kynjo/DRUM_2026_AI/tablesESP32_E.h

//  Tables V4

//This table id compatible with 20000.00 Hz. sampling rate
//Envelope frequency tuning word vs. MIDI range value [0-127]
const uint16_t EFTWS[]={
0x0371,0x0340,0x0311,0x02E5,0x02BB,0x0294,0x026F,0x024C,0x022B,0x020C,0x01EE,0x01D3,0x01B8,0x01A0,0x0188,0x0172,
0x015D,0x014A,0x0137,0x0126,0x0115,0x0106,0x00F7,0x00E9,0x00DC,0x00D0,0x00C4,0x00B9,0x00AE,0x00A5,0x009B,0x0093,
0x008A,0x0083,0x007B,0x0074,0x006E,0x0068,0x0062,0x005C,0x0057,0x0052,0x004D,0x0049,0x0045,0x0041,0x003D,0x003A,
0x0037,0x0034,0x0031,0x002E,0x002B,0x0029,0x0026,0x0024,0x0022,0x0020,0x001E,0x001D,0x001B,0x001A,0x0018,0x0017,
0x0015,0x0014,0x0013,0x0012,0x0011,0x0010,0x000F,0x000E,0x000D,0x000D,0x000C,0x000B,0x000A,0x000A,0x0009,0x0009,
0x0008,0x0008,0x0007,0x0007,0x0006,0x0006,0x0006,0x0005,0x0005,0x0005,0x0004,0x0004,0x0004,0x0004,0x0003,0x0003,
0x0003,0x0003,0x0003,0x0002,0x0002,0x0002,0x0002,0x0002,0x0002,0x0002,0x0001,0x0001,0x0001,0x0001,0x0001,0x0001,
0x0001,0x0001,0x0001,0x0001,0x0001,0x0001,0x0000,0x0000,0x0000,0x0000,0x0000,0x0000,0x0000,0x0000,0x0000,0x0000,
};

//Voice frequency tuning word vs. MIDI note [0-127]
const uint16_t PITCHS[]={
0x001A,0x001C,0x001E,0x001F,0x0021,0x0023,0x0025,0x0028,0x002A,0x002D,0x002F,0x0032,0x0035,0x0038,0x003C,0x003F,
0x0043,0x0047,0x004B,0x0050,0x0055,0x005A,0x005F,0x0065,0x006B,0x0071,0x0078,0x007F,0x0087,0x008F,0x0097,0x00A0,
0x00AA,0x00B4,0x00BE,0x00CA,0x00D6,0x00E3,0x00F0,0x00FE,0x010E,0x011E,0x012F,0x0141,0x0154,0x0168,0x017D,0x0194,
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
};

const signed char* wtables[16]={
SinTable,
TriangleTable,
SquareTable,
SawTable,
RampTable,
NoiseTable,
PhasorTable,
AdditiveTable,
SubBassWave,
WN1Table,
WN2Table,
WN3Table,
WN4Table,
WN5Table,
WN6Table,
WN7Table
};

const char* wenvs[5]={
Env0,
Env1,
Env2,
Env3,
Env4
};
